jncronin/gk/gk-pcbv4/stls/gkv4-bottom.stl

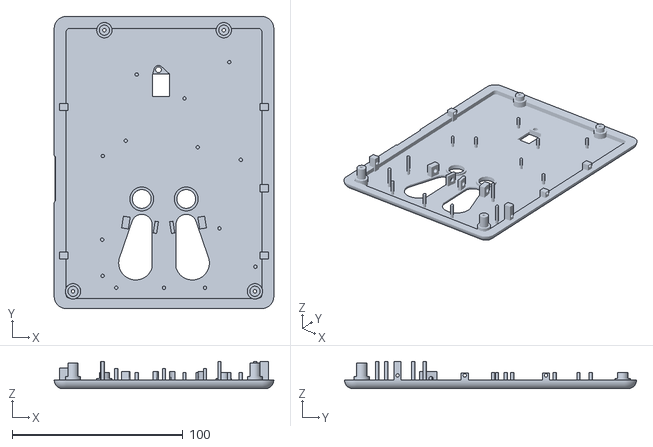
[picture p26: CAD file, 2026-03-30]
gk-pcbv4/stls/gkv4-bottom.stl
128.7 x 171.1 x 16.0
