jncronin/gk/gk-pcbv4/stls/menu inlay/front_button_crow_mask_top.stl

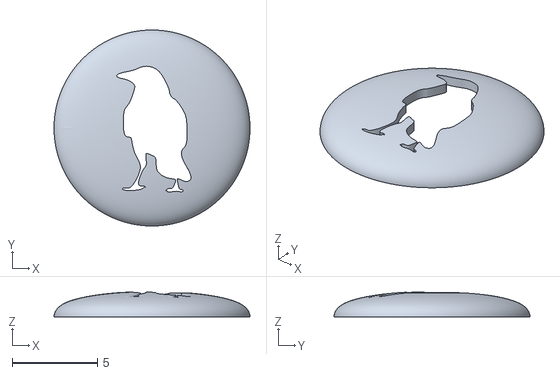
[picture p27: CAD file, 2026-03-17]
gk-pcbv4/stls/menu inlay/front_button_crow_mask_top.stl
11.5 x 11.5 x 1.47
