jncronin/gk/gk-pcbv3/gk-pcbv3/dpad.stl

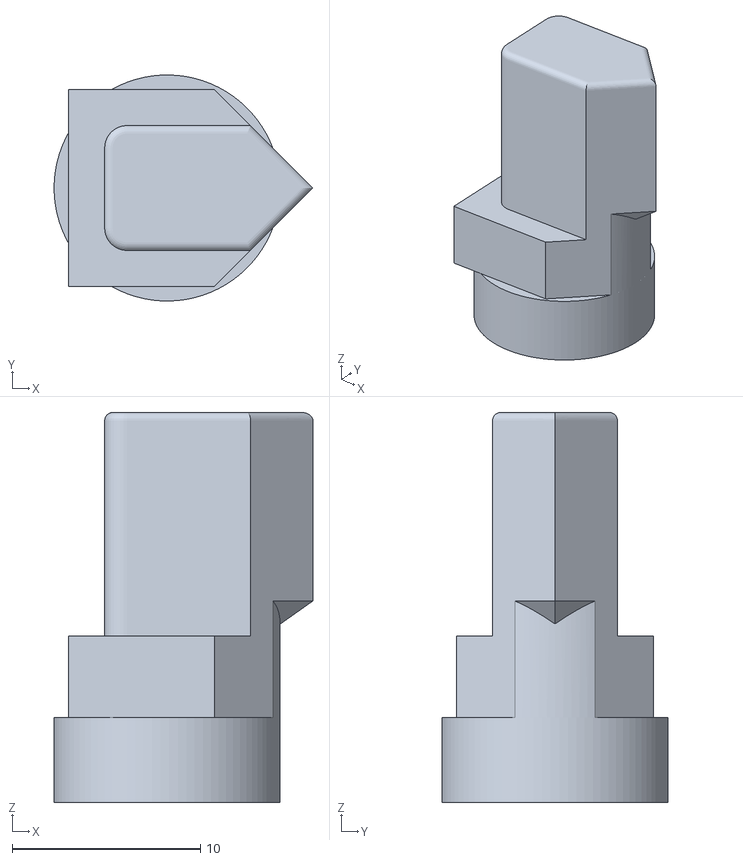
[picture p28: CAD file, 2025-01-18]
gk-pcbv3/gk-pcbv3/dpad.stl
13.7 x 12.0 x 20.7
