jncronin/gk/gk-pcbv4/gk/button_front.stl

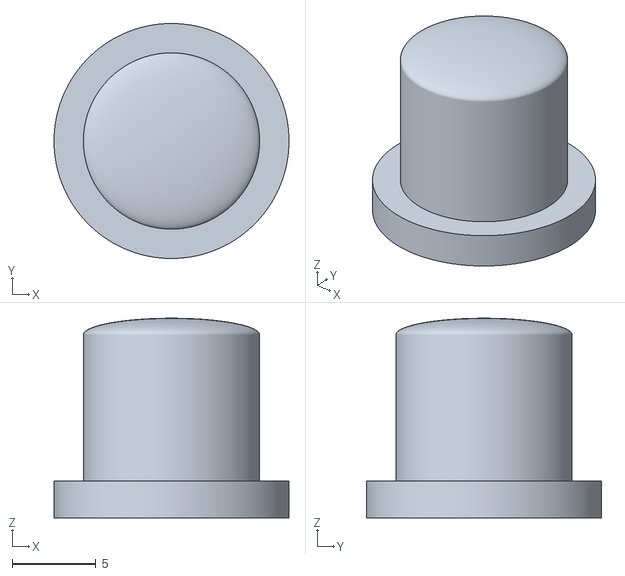
[picture p29: CAD file, 2026-05-26]
gk-pcbv4/gk/button_front.stl
14.0 x 14.0 x 11.9
