jncronin/gk/gk-pcbv4/stls/buttons/trigger.stl

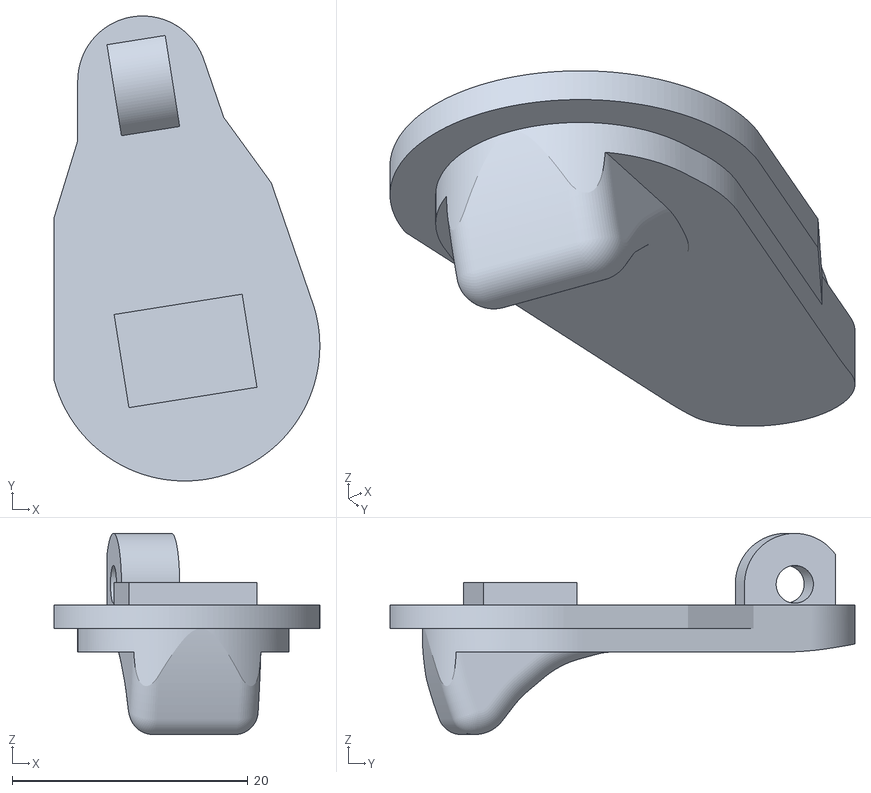
[picture p30: CAD file, 2026-03-30]
gk-pcbv4/stls/buttons/trigger.stl
22.5 x 39.4 x 17.1
