jncronin/gk/gk-pcbv3/gk-pcbv3/button power.stl

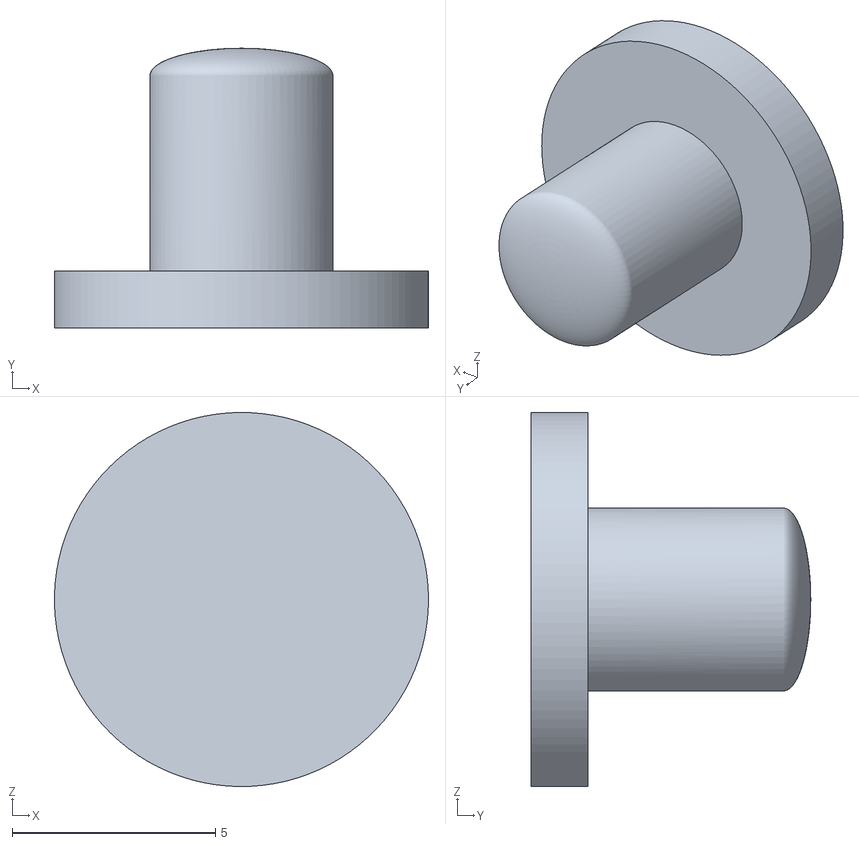
[picture p31: CAD file, 2025-01-18]
gk-pcbv3/gk-pcbv3/button power.stl
9.20 x 6.88 x 9.20
