jncronin/gk/gk-pcbv4/gk/button_back.stl

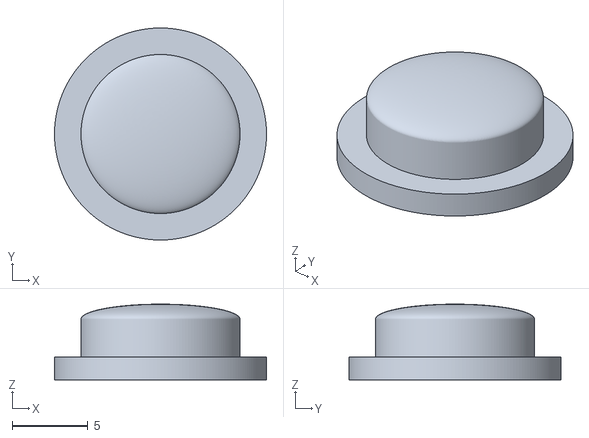
[picture p32: CAD file, 2026-05-26]
gk-pcbv4/gk/button_back.stl
14.0 x 14.0 x 5.00
