jncronin/gk/gk-pcbv4/stls/buttons/side_button.stl

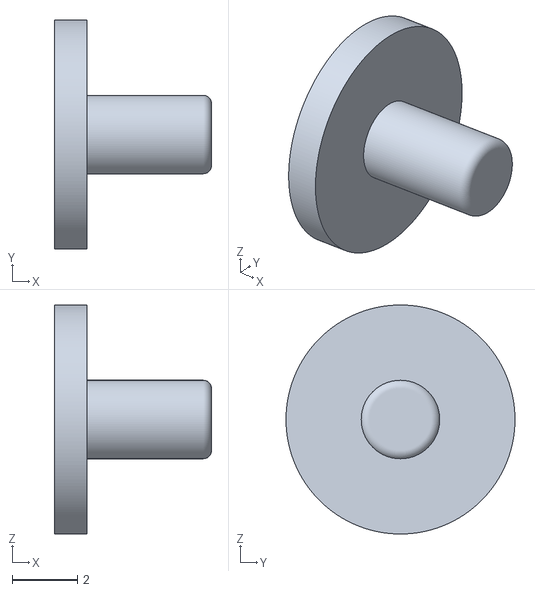
[picture p33: CAD file, 2026-03-30]
gk-pcbv4/stls/buttons/side_button.stl
4.80 x 7.00 x 7.00
