jncronin/gk/gk-pcbv3/gk-pcbv3/button x.stl

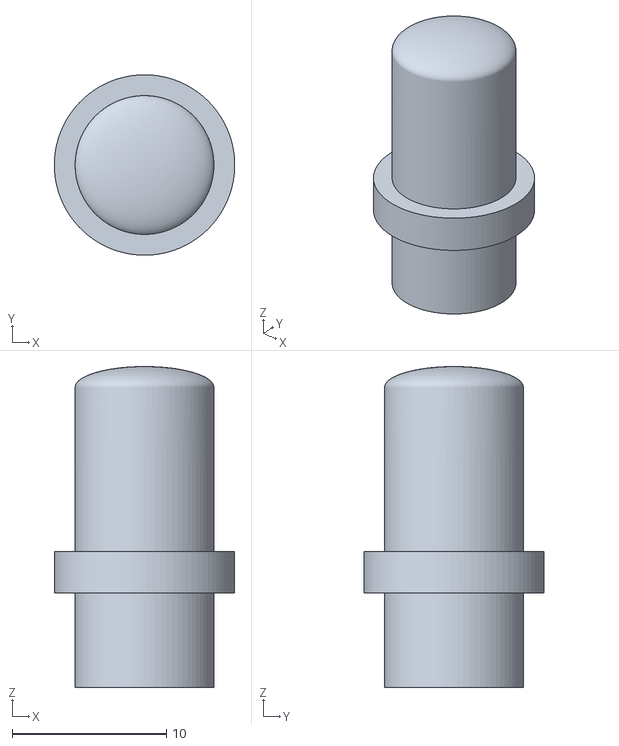
[picture p34: CAD file, 2025-01-13]
gk-pcbv3/gk-pcbv3/button x.stl
11.7 x 11.7 x 20.8
