jncronin/gk/gk-pcbv4/stls/buttons/abxy_button.stl

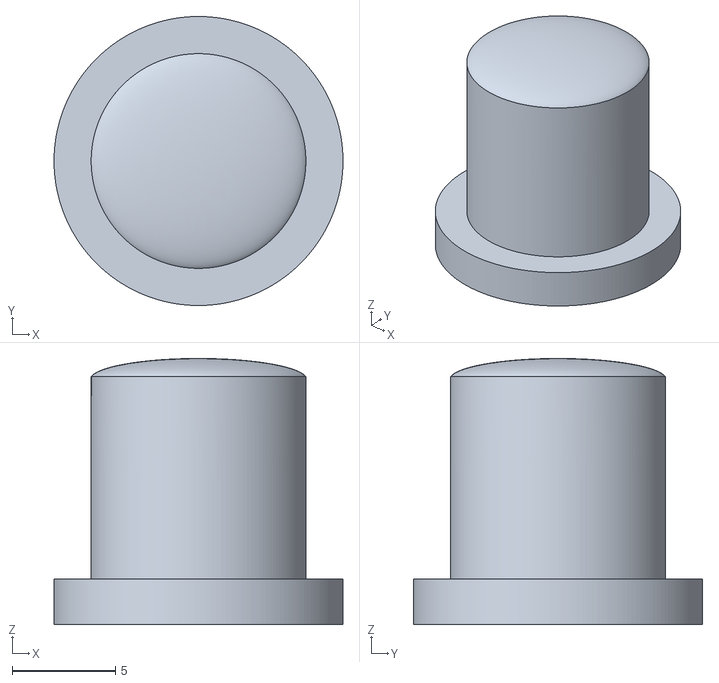
[picture p35: CAD file, 2026-03-30]
gk-pcbv4/stls/buttons/abxy_button.stl
14.0 x 14.0 x 12.9
