jncronin/gk/gk-pcbv3/gk-pcbv3/dpad left.stl

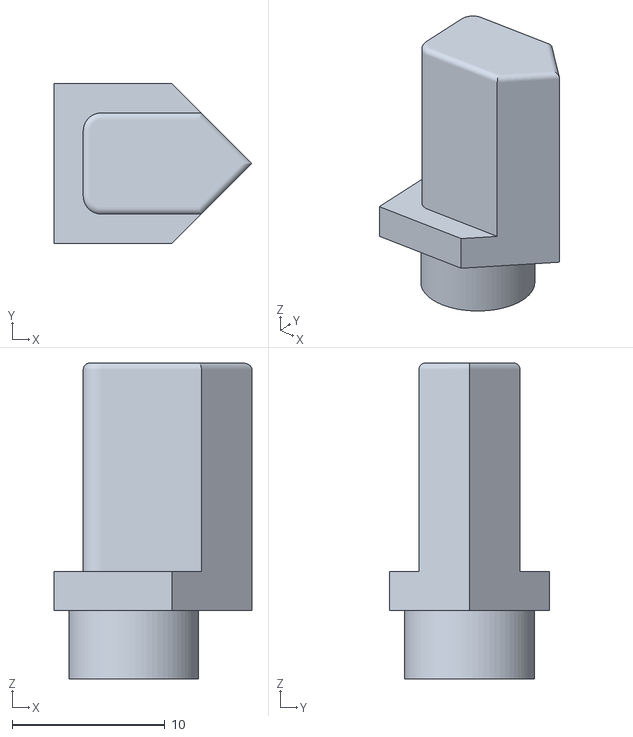
[picture p36: CAD file, 2025-01-13]
gk-pcbv3/gk-pcbv3/dpad left.stl
13.0 x 10.5 x 20.7
