jncronin/gk/gk-pcbv4/gk/button_dpad.stl

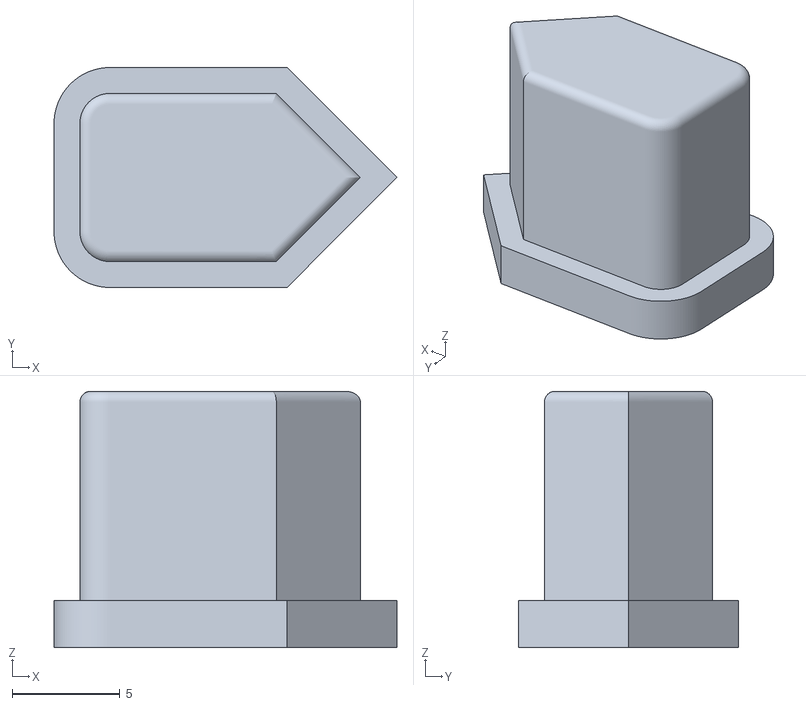
[picture p37: CAD file, 2026-05-26]
gk-pcbv4/gk/button_dpad.stl
15.9 x 10.2 x 11.9
