jncronin/gk/gk-pcbv4/stls/buttons/start_select.stl

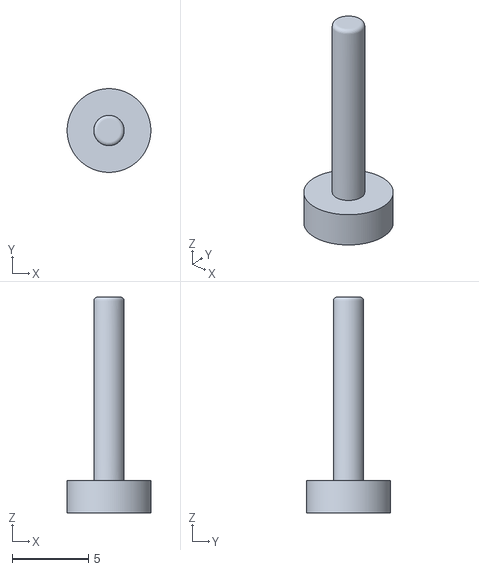
[picture p38: CAD file, 2026-03-30]
gk-pcbv4/stls/buttons/start_select.stl
5.50 x 5.50 x 14.2
