jncronin/gk/gk-pcbv3/gk-pcbv3/screen support.stl

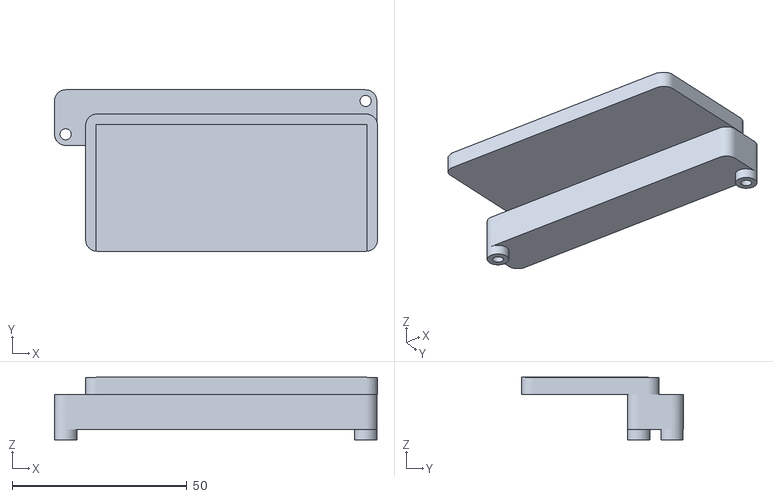
[picture p39: CAD file, 2024-11-11]
gk-pcbv3/gk-pcbv3/screen support.stl
92.3 x 46.1 x 18.0
