jncronin/gk/gk-pcbv4/gk/button_start_select.stl

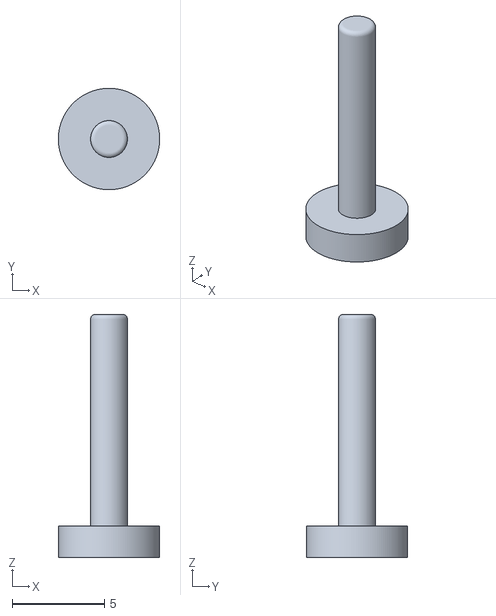
[picture p40: CAD file, 2026-05-26]
gk-pcbv4/gk/button_start_select.stl
5.50 x 5.50 x 13.2
