jncronin/gk/gk-pcbv4/stls/buttons/menu_button_with_inlay.stl

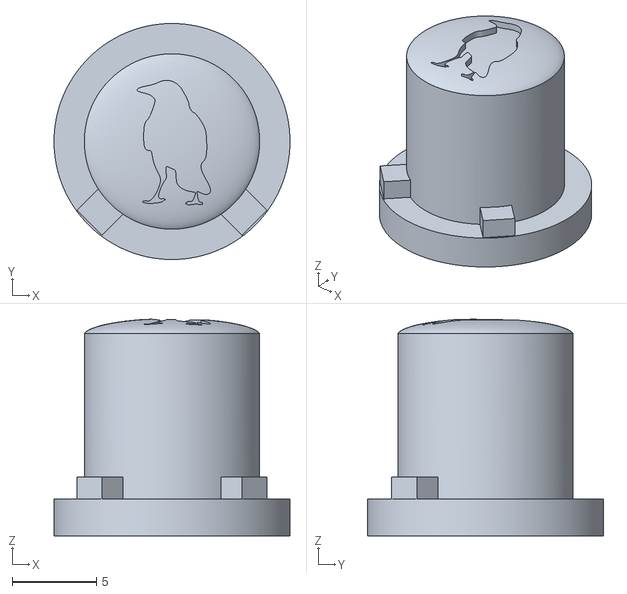
[picture p41: CAD file, 2026-03-30]
gk-pcbv4/stls/buttons/menu_button_with_inlay.stl
14.0 x 14.0 x 12.9
