jncronin/gk/gk-pcbv4/gk/v2 pcb outline.dxf

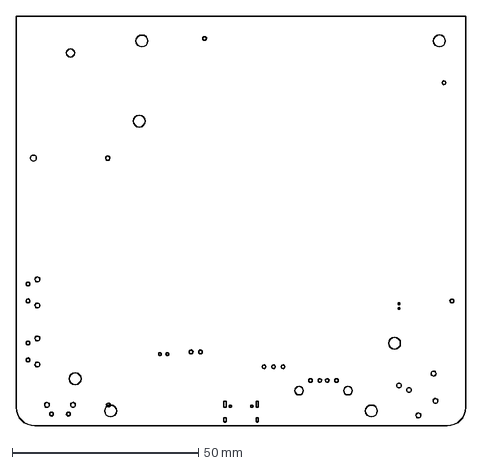
[picture p42: CAD file, 2026-03-11]
gk-pcbv4/gk/v2 pcb outline.dxf
120.7 x 110.0 mm
