jncronin/gk/gk-pcbv4/stls/buttons/menu_button.stl

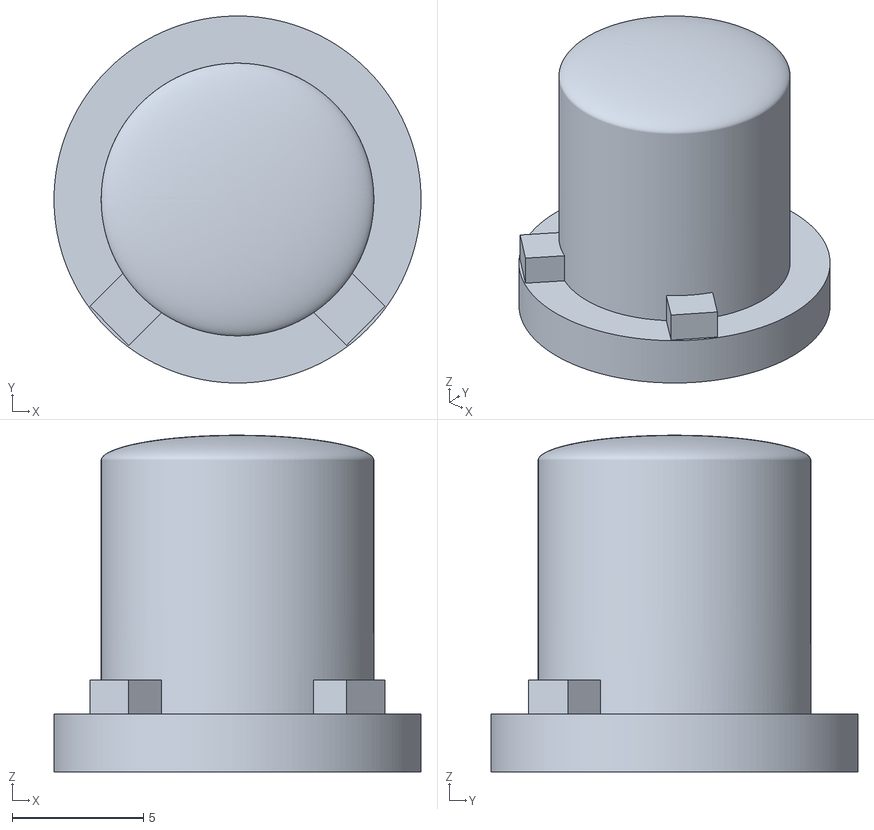
[picture p43: CAD file, 2026-03-30]
gk-pcbv4/stls/buttons/menu_button.stl
14.0 x 14.0 x 12.8
