jncronin/gk/gk-pcbv4/gk/screen_support_v4.stl

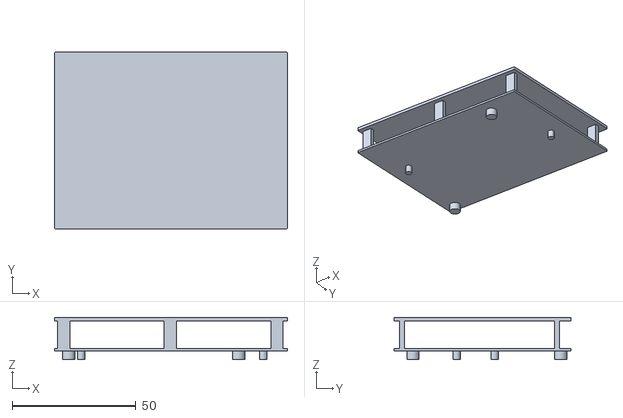
[picture p44: CAD file, 2026-02-03]
gk-pcbv4/gk/screen_support_v4.stl
94.0 x 71.5 x 17.0
