jncronin/gk/gk-pcbv3/gk-pcbv3/pwrbtn.asc

C1: cap; 100n
M1: nmos; N7002
M2: nmos; N7002
M3: nmos; N7002
M4: nmos; N7002
R1: res; 10k
R2: res; 10k
R3: res; 100k
R4: res; 100k
R5: res; 10k
R6: res; 100k
S1: sw
V1: voltage; 5
V2: voltage; PULSE(0 1 0.1 0.020 0.020 0.1 0.2 20)
V3: voltage; PULSE(0 3.3 0.01 0.0001 0.0001 0.01 0.02 200)
V4: voltage; 3.3
Named nets: 0, filt, vregin, vregen, mcu_pwr_en, btn_mcu_onoff, vcc
.tran 1
.model sw SW(Ron=0.001 Roff=100Meg Vt=0.5 Vh=0.01)
*---------- 2N7002 Spice Model ----------
.SUBCKT N7002 10 20 30 
*     TERMINALS:  D  G  S
M1 1 2 3 3 NMOS L = 1E-006 W = 1E-006 
RD 10 1 0.976 
RS 30 3 0.001 
RG 20 2 160.6 
CGS 2 3 2E-011 
EGD 12 0 2 1 1 
VFB 14 0 0 
FFB 2 1 VFB 1 
CGD 13 14 5.9E-011 
R1 13 0 1 
D1 12 13 DLIM 
DDG 15 14 DCGD 
R2 12 15 1 
D2 15 0 DLIM 
DSD 3 10 DSUB 
.MODEL NMOS NMOS LEVEL = 3 VMAX = 1E+006 ETA = 0 VTO = 2.154 
+ TOX = 6E-008 NSUB = 1E+016 KP = 0.4654 KAPPA = 1E-015 U0 = 400 
.MODEL DCGD D CJO = 1.2E-011 VJ = 0.6 M = 0.6 
.MODEL DSUB D IS = 6.808E-010 N = 1.576 RS = 0.1408 BV = 72 CJO = 8E-012 VJ = 0.8 M = 0.6474 
.MODEL DLIM D IS = 0.0001 
.ENDS
*Diodes N7002 Spice Model v0 Last Revised 2017/2/9
*ZETEX BSS84 Spice Model v1.1 Last Revised 3/5/00
    *              
    .SUBCKT BSS84 3 4 5
    * NODES: DRAIN GATE SOURCE
    M1 3 2 5 5 MOD1
    RG 4 2 167
    RL 3 5 50E6
    C1 2 5 26P
    C2 3 2 4P 
    D1 3 5 DIODE1
    *
    .MODEL MOD1 PMOS VTO=-1.709 RS=3.091 RD=0.979 IS=1E-15 KP=0.146
    +CBD=12P PB=1
    .MODEL DIODE1 D IS=1.072E-13 RS=0.527 N=1.077
    .ENDS BSS84
    *
    *$
    *
