jncronin/gk/Firmware-v4/gkos/src/process.cpp

#include "process.h"
#include "pmem.h"
#include "vmem.h"
#include "thread.h"
#include "screen.h"
#include "ipi.h"
#include "cleanup.h"
#include "process_interface.h"
#include "_gk_memaddrs.h"
#include "_gk_scancodes.h"
#include "syscalls_int.h"
#include "supervisor.h"
#include "cm33_interface.h"
#include "cpu.h"
#include <atomic>

#define DEBUG_PROCESS_PAGES     1

static std::atomic<pid_t> focus_process = 0;
extern PProcess p_gksupervisor;

PProcess Process::Create(const std::string &_name, bool _is_privileged, PProcess parent)
{
    auto ret = ProcessList.Create();

    ret->name = _name;
    ret->is_privileged = _is_privileged;

    // don't allow unprivileged processes to create privileged ones
    if(parent && parent->is_privileged == false)
        ret->is_privileged = false;

    if(!ret->is_privileged)
    {
        // generate a user space paging setup
        auto ttbr0_reg = Pmem.acquire(VBLOCK_64k);
        if(ttbr0_reg.valid == false)
        {
            klog("Process: could not allocate ttbr0\n");
            while(true);
        }
        quick_clear_64((void *)PMEM_TO_VMEM(ttbr0_reg.base));
        ((volatile uint64_t *)PMEM_TO_VMEM(ttbr0_reg.base))[8191] = process_highest_pt.base |
            PAGE_ACCESS | DT_PT;

        {
            CriticalGuard cg(ret->owned_pages.sl);
            ret->owned_pages.add(ttbr0_reg);
        }

        ret->user_mem = std::make_unique<userspace_mem_t>();
        {
            MutexGuard cg(ret->user_mem->m);
            ret->user_mem->ttbr0 = ttbr0_reg.base | ((uint64_t)ret->id << 48);
        }
    }

    // inherit fds + environ
    if(parent)
    {
        {
            CriticalGuard cg(ret->open_files.sl, parent->open_files.sl);
            ret->open_files.f = parent->open_files.f;
        }

        {
            CriticalGuard cg(ret->env.sl, parent->env.sl);
            ret->env.envs = parent->env.envs;
        }

        ret->ppid = parent->id;
        ProcessList.SetPPID(ret->id, parent->id);
    }

    ret->window_title = _name;

    return ret;
}

void Process::owned_pages_t::add(const PMemBlock &b, bool is_gpu)
{
    std::shared_ptr<shared_page> sp = nullptr;
    auto start = b.base & ~(VBLOCK_64k - 1ULL);
    auto end = (b.base + b.length + (VBLOCK_64k - 1ULL)) & ~(VBLOCK_64k - 1ULL);
    auto length = end - start;

    if(b.is_shared)
    {
        klog("process: shared pages not yet implemented\n");
    }
    if(is_gpu)
    {
        auto ret = gpu_pages.p.AllocFixed({ (uintptr_t)start, (uintptr_t)length }, std::move(sp));
        if(ret == gpu_pages.p.end())
        {
            klog("process: failed to add pages %llx - %llx to gpu list: already present.  Dump and backtrace follows.\n",
                start, start + length);

            gpu_pages.dump();
            backtrace();
        }
        else
        {
#if DEBUG_OWNED_PAGES
            klog("process: ADDED %llx - %llx to gpu list\n", start, start + length);
#endif
            gpu_pages.npages += length / PAGE_SIZE;
        }
        return;
    }
    else if(b.length != PAGE_SIZE || b.is_shared)
    {
        auto ret = other_pages.p.AllocFixed({ (uintptr_t)start, (uintptr_t)length }, std::move(sp));
        if(ret == other_pages.p.end())
        {
            klog("process: failed to add pages %llx - %llx to other list: already present.  Dump and backtrace follows.\n",
                start, start + length);

            other_pages.dump();
            backtrace();
        }
        else
        {
            other_pages.npages += length / PAGE_SIZE;
        }
        return;
    }

    while(start < end)
    {
        auto val = (uint32_t)(start >> 16);
        p.insert(val);
        start += VBLOCK_64k;
    }
}

void Process::owned_pages_t::release_all()
{
    for(auto curp : p)
    {
        auto addr = ((uint64_t)curp) << 16;
        PMemBlock pb;
        pb.base = addr;
        pb.is_shared = false;
        pb.length = VBLOCK_64k;
        pb.valid = true;
        Pmem.release(pb);
    }
    p.clear();

    for(auto l : { &other_pages, &gpu_pages })
    {
        for(auto iter = l->p.begin(); iter != l->p.end();)
        {
            if(iter->second)
            {
                // shared pages not handled yet
                iter++;
                continue;
            }

            PMemBlock pb;
            pb.base = iter->first.start;
            pb.length = iter->first.length;
            pb.is_shared = false;
            pb.valid = true;
            Pmem.release(pb);

            l->npages -= iter->first.length / PAGE_SIZE;
            iter = l->p.erase(iter);
        }
    }
}

void Process::owned_pages_t::release(const PMemBlock &pb)
{
    if(!pb.valid)
        return;
    
    for(auto l : { &other_pages, &gpu_pages })
    {
        auto is_alloc = l->p.IsAllocated(pb.base);
        if(is_alloc == l->p.end())
            continue;

#if DEBUG_OWNED_PAGES
        if(l == &gpu_pages)
        {
            klog("process: REMOVED %llx - %llx from gpu list\n", pb.base, pb.base + pb.length);
        }
#endif
        
        if(is_alloc->first.start != pb.base ||
            is_alloc->first.length != pb.length)
        {
            klog("process: WARN: release only a portion off whole allocated physmem area\n");
        }
        if(is_alloc->second)
        {
            klog("process: WARN: shared pages not yet implemented\n");
        }
        l->p.erase(is_alloc);
        l->npages -= pb.length / PAGE_SIZE;
        return;
    }

    bool released_all = true;
    for(auto pstart = pb.base; pstart < (pb.base + pb.length); pstart += PAGE_SIZE)
    {
        auto is_alloc = p.find(pstart >> 16);
        if(is_alloc != p.end())
        {
            p.erase(is_alloc);
        }
        else
        {
            released_all = false;
        }
    }

    if(!released_all)
    {
        klog("process: WARN: tried to release memory %llx - %llx which we have no record of\n",
            pb.base, pb.base + pb.length);
    }
}

bool Process::owned_pages_t::contains(uintptr_t addr, uintptr_t len)
{
    if(len > VBLOCK_64k)
    {
        auto ret = true;

        for(auto i = 0ull; i < len; i += VBLOCK_64k)
        {
            if(!contains(addr + i))
            {
                ret = false;
                break;
            }
        }

        return ret;
    }

    if(p.find(addr >> 16) != p.end())
        return true;
    else if(gpu_pages.p.IsAllocated(addr) != gpu_pages.p.end())
        return true;
    else if(other_pages.p.IsAllocated(addr) != other_pages.p.end())
        return true;

    return false;
}

void Process::owned_pages_t::owned_page_list::dump()
{
    for(const auto &cpp : p)
    {
        const auto &cp = cpp.first;
        klog("PMEM_DUMP: %p - %p\n", (void *)cp.start, (void *)cp.end());
    }
}

void Process::Kill(id_t pid, int rc)
{
    CriticalGuard cg(ProcessList.sl);
    auto p = ProcessList._get(pid);
    if(!p.v)
    {
        klog("process: request to kill a process (%u) that doesn't exist", pid);
        return;
    }

    // restore focus process, if applicable
    if(GetFocusPid() == pid)
    {
        auto pparent = ProcessList._get(p.v->ppid);
        if(pparent.v)
        {
            SetFocusProcess(pparent.v);
        }
    }

    klog("syscall_kill: kill pid %d, rc %d\n", pid, rc);
    ProcessList._setexitcode(pid, rc);
    cg.unlock();

    id_t cur_thread_to_kill = 0;
    for(auto t : p.v->threads)
    {
        if(t == GetCurrentThreadForCore()->id)
        {
            cur_thread_to_kill = t;
            continue;
        }
        Thread::Kill(t, (void *)0);
    }

    // Wake up any waiting threads
    for(auto t_wait : p.v->waiting_threads)
    {
        auto pt_wait = ThreadList.Get(t_wait);
        klog("syscall_kill: kill pid %d, wakeup %d (%s)\n", pid, t_wait, pt_wait.v == nullptr ? "dead thread" :
            pt_wait.v->name.c_str());
        if(pt_wait.v)
        {
            pt_wait.v->blocking.unblock();
        }
    }

    CleanupQueue.Push(cleanup_message { .is_thread = false, .id = pid });

    // kill the current thread last
    if(cur_thread_to_kill)
    {
        Thread::Kill(cur_thread_to_kill, (void *)0);
    }
}

bool Process::check_process_pages_vs_ttbr()
{
    CriticalGuard cg(sl, owned_pages.sl);
    if(!user_mem)
        return true;

    MutexGuard mg(user_mem->m);

    bool ret = true;

    if(!owned_pages.contains(user_mem->ttbr0 & PAGE_PADDR_MASK))
    {
        ret = false;
        klog("process: owned_pages does not include ttbr0 %llx\n", user_mem->ttbr0 & PAGE_PADDR_MASK);
    }

    // iterate pd entries
    auto pd = (uint64_t *)PMEM_TO_VMEM(user_mem->ttbr0 & PAGE_PADDR_MASK);
    for(auto pdi = 0u; pdi < 8191u; pdi++)  // avoid last entry (process interface stuff)
    {
        auto pde = pd[pdi];
        auto pde_format = pde & 0x3;

        if(pde_format == DT_BLOCK)
        {
            if(!owned_pages.contains(pde & PAGE_PADDR_MASK, VBLOCK_512M))
            {
                ret = false;
                klog("process: owned_pages does not include block %llx for vaddr %llx\n",
                    pde & PAGE_PADDR_MASK,
                    pdi * VBLOCK_512M);
            }
        }
        else if(pde_format == DT_PT)
        {
            if(!owned_pages.contains(pde & PAGE_PADDR_MASK))
            {
                ret = false;
                klog("process: owned_pages does not include page table %llx\n",
                    pde & PAGE_PADDR_MASK);
            }

            // iterate pt entries
            auto pt = (uint64_t *)PMEM_TO_VMEM(pde & PAGE_PADDR_MASK);

            for(auto pti = 0u; pti < 8192u; pti++)
            {
                auto pte = pt[pti];
                auto pte_format = pte & 0x3;

                if(pte_format == DT_PAGE)
                {
                    if(!owned_pages.contains(pte & PAGE_PADDR_MASK))
                    {
                        ret = false;
                        klog("process: owned_pages does not include page %llx for vaddr %llx\n",
                            pte & PAGE_PADDR_MASK,
                            pdi * VBLOCK_512M + pti * VBLOCK_64k);
                    }
                }
            }
        }
    }

    if(!ret)
    {
        user_mem->vblocks.Traverse([](MemBlock &mb)
        {
            klog("mmap: %p - %p, %s%s%s%s %llx %llx\n",
                (void *)mb.b.data_start(),
                (void *)mb.b.data_end(),
                mb.b.user ? "U" : " ",
                mb.b.write ? "W" : " ",
                mb.b.exec ? "X" : " ",
                (mb.f == nullptr) ? "" : " FILE",
                mb.foffset,
                mb.flen);
            return 0;
        });
    }

    return ret;
}

Process::~Process()
{
    // This should only be called by the cleanup thread finally deleting the entry in ProcessList
    klog("process: %u:%s destructor called\n", id, name.c_str());

#if DEBUG_PROCESS_PAGES
    check_process_pages_vs_ttbr();
#endif

    // Release resources
    owned_pages.release_all();

    owned_conditions.clear();
    owned_mutexes.clear();
    owned_rwlocks.clear();
    owned_semaphores.clear();
}

extern PMemBlock process_kernel_info_page;

static void set_joystick_mapping(char stick_map, int16_t *x, int16_t *y)
{
    auto kinfo = (gk_kernel_info *)PMEM_TO_VMEM(process_kernel_info_page.base);

    if((stick_map >= GK_STICK_JOY0) && (stick_map <= GK_STICK_JOY3))
    {
        auto stick_id = (unsigned int)(stick_map - GK_STICK_JOY0);
        auto x_axis_id = stick_id * 2;
        auto y_axis_id = x_axis_id + 1;

        kinfo->joystick_axes[x_axis_id] = x;
        kinfo->joystick_axes[y_axis_id] = y;

        if((y_axis_id + 1) > kinfo->joystick_naxes)
        {
            kinfo->joystick_naxes = y_axis_id + 1;
        }
    }
    else if(stick_map == GK_STICK_MOUSE)
    {
        kinfo->mouse_axes[0] = x;
        kinfo->mouse_axes[1] = y;
    }
}

int SetFocusProcess(PProcess p)
{
    focus_process = p->id;

    // clear screen on process switch
    screen_clear_all_userspace();

    // update userspace input mapping
    auto kinfo = (gk_kernel_info *)PMEM_TO_VMEM(process_kernel_info_page.base);

    kinfo->joystick_naxes = 0;
    memset(kinfo->joystick_axes, 0, sizeof(kinfo->joystick_axes));
    memset(kinfo->mouse_axes, 0, sizeof(kinfo->mouse_axes));

    set_joystick_mapping(p->keymap.left_stick & GK_STICK_LOW_MASK,
        (int16_t *)(GK_JOYSTICK_ADDRESS),
        (int16_t *)(GK_JOYSTICK_ADDRESS + 4));
    set_joystick_mapping(p->keymap.right_stick & GK_STICK_LOW_MASK,
        (int16_t *)(GK_JOYSTICKB_ADDRESS),
        (int16_t *)(GK_JOYSTICKB_ADDRESS + 4));
    set_joystick_mapping(p->keymap.tilt_stick & GK_STICK_LOW_MASK,
        (int16_t *)(GK_TILT_ADDRESS),
        (int16_t *)(GK_TILT_ADDRESS + 4));
    set_joystick_mapping(p->keymap.throttle_stick & GK_STICK_LOW_MASK,
        (int16_t *)(GK_THROTTLE_ADDRESS + 4),
        (int16_t *)(GK_THROTTLE_ADDRESS + 4));

    cm33_set_left_stick_4way((p->keymap.left_stick & GK_STICK_4WAY) != 0);
    cm33_set_right_stick_4way((p->keymap.right_stick & GK_STICK_4WAY) != 0);
    cm33_set_tilt_stick_4way((p->keymap.tilt_stick & GK_STICK_4WAY) != 0);

    unsigned int nbuttons = 0;
    for(auto i = 0U; i < GK_NUMKEYS; i++)
    {
        auto scancode = p->keymap.gamepad_to_scancode[i];
        if(scancode >= GK_GAMEPAD_BUTTON && scancode <= GK_GAMEPAD_END)
        {
            auto btn_id = scancode - GK_GAMEPAD_BUTTON;
            if(btn_id < 64 && (btn_id + 1U) > nbuttons)
            {
                nbuttons = btn_id + 1U;
            }
        }
    }
    kinfo->joystick_buttons = 0;
    kinfo->joystick_nbuttons = nbuttons;

    // enable/disable tilt if appropriate
    if(p->keymap.tilt_stick == GK_STICK_DIGITAL &&
        p->keymap.gamepad_to_scancode[GK_KEYTILTLEFT] == 0 &&
        p->keymap.gamepad_to_scancode[GK_KEYTILTRIGHT] == 0 &&
        p->keymap.gamepad_to_scancode[GK_KEYTILTUP] == 0 &&
        p->keymap.gamepad_to_scancode[GK_KEYTILTDOWN] == 0)
    {
        cm33_set_tilt(false);
    }
    else
    {
        cm33_set_tilt(true);
    }

    // enable/disable ctp
    if(p->keymap.touch_is_mouse || supervisor_is_active())
    {
        cm33_set_touch(true);
    }
    else
    {
        cm33_set_touch(false);
    }

    // set cm33 to batch mouse move events, if applicable
    cm33_set_left_stick_mouse(p->keymap.left_stick == GK_STICK_MOUSE);
    cm33_set_right_stick_mouse(p->keymap.right_stick == GK_STICK_MOUSE);
    cm33_set_tilt_stick_mouse(p->keymap.tilt_stick == GK_STICK_MOUSE);
    cm33_set_throttle_stick_mouse(p->keymap.throttle_stick == GK_STICK_MOUSE);

    // enable throttle detents, if applicable
    if(p->keymap.throttle_stick >= GK_STICK_THROTTLE_DETENT && 
        p->keymap.throttle_stick <= GK_STICK_THROTTLE_DETENT_MAX)
    {
        cm33_set_throttle_stick_detent(true, p->keymap.throttle_stick - GK_STICK_THROTTLE_DETENT + 1);
    }
    else
    {
        cm33_set_throttle_stick_detent(false, 0);
    }

    // restore palette if used


    // update cpu freq
    if(p->cpu_freq != clock_get_cpu())
    {
        clock_set_cpu_and_vddcpu(p->cpu_freq);
    }

    // tell p_supervisor about it
    if(p_gksupervisor)
    {
        p_gksupervisor->events.Push({ .type = Event::event_type_t::CaptionChange });
    }

    return 0;
}

PProcess GetFocusProcess()
{
    return ProcessList.Get(focus_process).v;
}

id_t GetFocusPid()
{
    return focus_process;
}
